sidianneng/xiaomi_temp_humi/source_code/Core/Inc/EPD_Font.h

#ifndef _EPD_FONT_H_
#define _EPD_FONT_H_


//图片取模配置使用软件 PCtoLCD2002
//点阵格式:阴码
//取模走向:逆向(低位在前)
//取模方式:
//				 字符:列行式 C51格式 
//				 中文:逐行式 C51格式
//字符尺寸限制:字符宽度限制为8的倍数

const unsigned char asc2_2412[][36]={	  
{0x00,0x00,0x00,0x00,0x00,0x00,0x00,0x00,0x00,0x00,0x00,0x00,0x00,0x00,0x00,0x00,0x00,0x00,0x00,0x00,0x00,0x00,0x00,0x00,0x00,0x00,0x00,0x00,0x00,0x00,0x00,0x00,0x00,0x00,0x00,0x00},/*" ",0*/
{0x00,0x00,0x00,0x00,0x00,0xF0,0xF0,0xF0,0x00,0x00,0x00,0x00,0x00,0x00,0x00,0x00,0x00,0x01,0x7F,0x01,0x00,0x00,0x00,0x00,0x00,0x00,0x00,0x00,0x00,0x1C,0x1C,0x1C,0x00,0x00,0x00,0x00},/*"!",1*/
{0x00,0x00,0x80,0x60,0x30,0x1C,0x8C,0x60,0x30,0x1C,0x0C,0x00,0x00,0x00,0x00,0x00,0x00,0x00,0x00,0x00,0x00,0x00,0x00,0x00,0x00,0x00,0x00,0x00,0x00,0x00,0x00,0x00,0x00,0x00,0x00,0x00},/*""",2*/
{0x00,0x00,0x00,0xE0,0x00,0x00,0x00,0x00,0x00,0xE0,0x00,0x00,0x00,0x86,0xE6,0x9F,0x86,0x86,0x86,0x86,0xE6,0x9F,0x86,0x00,0x00,0x01,0x1F,0x01,0x01,0x01,0x01,0x01,0x1F,0x01,0x01,0x00},/*"#",3*/
{0x00,0x00,0x80,0xC0,0x60,0x20,0xF8,0x20,0xE0,0xC0,0x00,0x00,0x00,0x00,0x03,0x07,0x0C,0x18,0xFF,0x70,0xE1,0x81,0x00,0x00,0x00,0x00,0x07,0x0F,0x10,0x10,0x7F,0x10,0x0F,0x07,0x00,0x00},/*"$",4*/
{0x80,0x60,0x20,0x60,0x80,0x00,0x00,0x00,0xE0,0x20,0x00,0x00,0x0F,0x30,0x20,0x30,0x9F,0x70,0xDC,0x37,0x10,0x30,0xC0,0x00,0x00,0x00,0x10,0x0E,0x03,0x00,0x07,0x18,0x10,0x18,0x07,0x00},/*"%",5*/
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
0x00,0x00,0x00,0x00,0x00,0x00,0x00,0x00,0x00,0x00,0x00,0x00,0x00,0x00,0x00,0x00},/*")",9*/
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
};

#endif
