sidianneng/xiaomi_temp_humi/source_code/Core/Inc/config.h

#ifndef __CONFIG_H__
#define __CONFIG_H__

#ifdef __cplusplus
extern "C" {
#endif

#define MAIN_VERSION 0x00
#define SUB_VERSION 0x01

#define DEBUG_LOG 1 
#define MAX_LOG_BUF_LEN 32U

#ifdef __cplusplus
}
#endif

#endif
