sidianneng/xiaomi_temp_humi/source_code/Core/Inc/Pic.h

#ifndef _PIC_H_
#define _PIC_H_

const unsigned char gImage_2424_bt[72] = { /* 0X01,0X01,0X18,0X00,0X18,0X00, */
0X00,0X00,0X00,0X00,0X00,0X00,0X00,0X00,0X00,0X00,0X00,0X00,0X00,0X00,0X00,0X03,
0X00,0XC0,0X01,0X81,0X80,0X00,0XC3,0X00,0X00,0X66,0X00,0X00,0X3C,0X00,0X00,0X18,
0X00,0X7F,0XFF,0XFE,0XFF,0XFF,0XFF,0XC0,0X3C,0X03,0X60,0X66,0X06,0X30,0XC3,0X0C,
0X19,0X81,0X98,0X0F,0X00,0XF0,0X06,0X00,0X60,0X00,0X00,0X00,0X00,0X00,0X00,0X00,
0X00,0X00,0X00,0X00,0X00,0X00,0X00,0X00,};

const unsigned char gImage_2424_nobt[72] = { /* 0X01,0X01,0X18,0X00,0X18,0X00, */
0X00,0X00,0X00,0X00,0X00,0X00,0X00,0X00,0X00,0X00,0X00,0X00,0X00,0X00,0X00,0X00,
0X00,0X00,0X00,0X00,0X00,0X00,0X00,0X00,0X00,0X00,0X00,0X00,0X00,0X00,0X00,0X00,
0X00,0X00,0X00,0X00,0X00,0X00,0X00,0X00,0X00,0X00,0X00,0X00,0X00,0X00,0X00,0X00,
0X00,0X00,0X00,0X00,0X00,0X00,0X00,0X00,0X00,0X00,0X00,0X00,0X00,0X00,0X00,0X00,
0X00,0X00,0X00,0X00,0X00,0X00,0X00,0X00,};

const unsigned char gImage_2424_bat[72] = { /* 0X01,0X01,0X18,0X00,0X18,0X00, */
0X00,0X00,0X00,0X00,0X00,0X00,0X00,0XFE,0X00,0X00,0XFE,0X00,0X07,0XFF,0XC0,0X04,
0X00,0X40,0X04,0X00,0X40,0X04,0X00,0X40,0X04,0X00,0X40,0X04,0X00,0X40,0X04,0X00,
0X40,0X04,0X00,0X40,0X04,0X00,0X40,0X04,0X00,0X40,0X04,0X00,0X40,0X04,0X00,0X40,
0X04,0X00,0X40,0X05,0XFF,0X40,0X05,0XFF,0X40,0X05,0XFF,0X40,0X04,0X00,0X40,0X07,
0XFF,0XC0,0X03,0XFF,0X80,0X00,0X00,0X00,};

const unsigned char gImage_2424_nobat[72] = { /* 0X01,0X01,0X18,0X00,0X18,0X00, */
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
0X00,0X00,0X00,0X00,0X00,0X00,0X00,0X00,0X00,0X00,0X00,0X00,0X00,0X00,0X00,0X00,
0X00,0X00,0X00,0X00,0X00,0X00,0X00,0X00,0X1E,0X00,0X00,0X38,0X1F,0X80,0X01,0XF8,
0X0F,0XFF,0XFF,0XF0,0X01,0XFF,0XFF,0X80,0X00,0X1F,0XF8,0X00,0X00,0X00,0X00,0X00,
};

#endif
