sidianneng/xiaomi_temp_humi/source_code/Core/Src/usart.c

/**
  ******************************************************************************
  * @file    usart.c
  * @brief   This file provides code for the configuration
  *          of the USART instances.
  ******************************************************************************
  * @attention
  *
  * <h2><center>&copy; Copyright (c) 2024 STMicroelectronics.
  * All rights reserved.</center></h2>
  *
  * This software component is licensed by ST under BSD 3-Clause license,
  * the "License"; You may not use this file except in compliance with the
  * License. You may obtain a copy of the License at:
  *                        opensource.org/licenses/BSD-3-Clause
  *
  ******************************************************************************
  */

/* Includes ------------------------------------------------------------------*/
#include "usart.h"

/* USART2 init function */

void MX_USART2_UART_Init(void)
{

  LL_USART_InitTypeDef USART_InitStruct = {0};

  LL_GPIO_InitTypeDef GPIO_InitStruct = {0};

  /* Peripheral clock enable */
  LL_APB1_GRP1_EnableClock(LL_APB1_GRP1_PERIPH_USART2);

  /* Set USART1 clock source as HSI */
  LL_RCC_SetUSARTClockSource(LL_RCC_USART2_CLKSOURCE_HSI);

  LL_IOP_GRP1_EnableClock(LL_IOP_GRP1_PERIPH_GPIOA);
  /**USART2 GPIO Configuration
  PA2   ------> USART2_TX
  PA3   ------> USART2_RX
  */
  GPIO_InitStruct.Pin = LL_GPIO_PIN_2;
  GPIO_InitStruct.Mode = LL_GPIO_MODE_ALTERNATE;
  GPIO_InitStruct.Speed = LL_GPIO_SPEED_FREQ_VERY_HIGH;
  GPIO_InitStruct.OutputType = LL_GPIO_OUTPUT_PUSHPULL;
  GPIO_InitStruct.Pull = LL_GPIO_PULL_NO;
  GPIO_InitStruct.Alternate = LL_GPIO_AF_4;
  LL_GPIO_Init(GPIOA, &GPIO_InitStruct);

  GPIO_InitStruct.Pin = LL_GPIO_PIN_3;
  GPIO_InitStruct.Mode = LL_GPIO_MODE_ALTERNATE;
  GPIO_InitStruct.Speed = LL_GPIO_SPEED_FREQ_VERY_HIGH;
  GPIO_InitStruct.OutputType = LL_GPIO_OUTPUT_PUSHPULL;
  GPIO_InitStruct.Pull = LL_GPIO_PULL_NO;
  GPIO_InitStruct.Alternate = LL_GPIO_AF_4;
  LL_GPIO_Init(GPIOA, &GPIO_InitStruct);

  /* USART2 interrupt Init */
  NVIC_SetPriority(USART2_IRQn, 2);
  NVIC_EnableIRQ(USART2_IRQn);

  USART_InitStruct.BaudRate = 9600;
  USART_InitStruct.DataWidth = LL_USART_DATAWIDTH_8B;
  USART_InitStruct.StopBits = LL_USART_STOPBITS_1;
  USART_InitStruct.Parity = LL_USART_PARITY_NONE;
  USART_InitStruct.TransferDirection = LL_USART_DIRECTION_TX_RX;
  USART_InitStruct.HardwareFlowControl = LL_USART_HWCONTROL_NONE;
  USART_InitStruct.OverSampling = LL_USART_OVERSAMPLING_16;
  LL_USART_Init(USART2, &USART_InitStruct);
  LL_USART_ConfigAsyncMode(USART2);
  LL_USART_SetWKUPType(USART2, LL_USART_WAKEUP_ON_RXNE);
  LL_USART_Enable(USART2);
  /* USER CODE BEGIN USART2_Init 2 */

  LL_USART_EnableIT_RXNE(USART2);
  /* Polling USART initialisation */
  while((!(LL_USART_IsActiveFlag_TEACK(USART2))) || (!(LL_USART_IsActiveFlag_REACK(USART2))))
  { 
  }
  /* USER CODE END USART2_Init 2 */

}

/* USER CODE BEGIN 1 */
void PrepareUSARTToStopMode(void)
{

  /* Empty RX Fifo before entering Stop mode (Otherwise, characters already present in FIFO
     will lead to immediate wake up */
  while (LL_USART_IsActiveFlag_RXNE(USART2))
  {
    /* Read Received character. RXNE flag is cleared by reading of RDR register */
    LL_USART_ReceiveData8(USART2);
  }

  /* Clear OVERRUN flag */
  LL_USART_ClearFlag_ORE(USART2);

  /* Make sure that no USART transfer is on-going */ 
  while(LL_USART_IsActiveFlag_BUSY(USART2) == 1)
  {
  }
  /* Make sure that USART is ready to receive */   
  while(LL_USART_IsActiveFlag_REACK(USART2) == 0)
  {
  }

  /* Configure USART2 transfer interrupts : */
  /* Clear WUF flag and enable the UART Wake Up from stop mode Interrupt */
  LL_USART_ClearFlag_WKUP(USART2);
  LL_USART_EnableIT_WKUP(USART2);

  /* Enable Wake Up From Stop */
  LL_USART_EnableInStopMode(USART2);
}
/* USER CODE END 1 */

/************************ (C) COPYRIGHT STMicroelectronics *****END OF FILE****/
