sidianneng/xiaomi_temp_humi/source_code/Core/Src/i2c.c

/**
  ******************************************************************************
  * @file    i2c.c
  * @brief   This file provides code for the configuration
  *          of the I2C instances.
  ******************************************************************************
  * @attention
  *
  * <h2><center>&copy; Copyright (c) 2024 STMicroelectronics.
  * All rights reserved.</center></h2>
  *
  * This software component is licensed by ST under BSD 3-Clause license,
  * the "License"; You may not use this file except in compliance with the
  * License. You may obtain a copy of the License at:
  *                        opensource.org/licenses/BSD-3-Clause
  *
  ******************************************************************************
  */

/* Includes ------------------------------------------------------------------*/
#include "i2c.h"

/* I2C1 init function */
void MX_I2C1_Init(void)
{

  LL_I2C_InitTypeDef I2C_InitStruct = {0};

  LL_GPIO_InitTypeDef GPIO_InitStruct = {0};

  uint32_t timing = 0;

  LL_IOP_GRP1_EnableClock(LL_IOP_GRP1_PERIPH_GPIOA);
  /**I2C1 GPIO Configuration
  PA9   ------> I2C1_SCL
  PA10   ------> I2C1_SDA
  */
  GPIO_InitStruct.Pin = LL_GPIO_PIN_9;
  GPIO_InitStruct.Mode = LL_GPIO_MODE_ALTERNATE;
  GPIO_InitStruct.Speed = LL_GPIO_SPEED_FREQ_VERY_HIGH;
  GPIO_InitStruct.OutputType = LL_GPIO_OUTPUT_OPENDRAIN;
  GPIO_InitStruct.Pull = LL_GPIO_PULL_UP;
  GPIO_InitStruct.Alternate = LL_GPIO_AF_1;
  LL_GPIO_Init(GPIOA, &GPIO_InitStruct);

  GPIO_InitStruct.Pin = LL_GPIO_PIN_10;
  GPIO_InitStruct.Mode = LL_GPIO_MODE_ALTERNATE;
  GPIO_InitStruct.Speed = LL_GPIO_SPEED_FREQ_VERY_HIGH;
  GPIO_InitStruct.OutputType = LL_GPIO_OUTPUT_OPENDRAIN;
  GPIO_InitStruct.Pull = LL_GPIO_PULL_UP;
  GPIO_InitStruct.Alternate = LL_GPIO_AF_1;
  LL_GPIO_Init(GPIOA, &GPIO_InitStruct);

  /* Peripheral clock enable */
  LL_APB1_GRP1_EnableClock(LL_APB1_GRP1_PERIPH_I2C1);

  /* According to TRM, I2C clock must be HSI if it can wakeup STOP mode */
  LL_RCC_SetI2CClockSource(LL_RCC_I2C1_CLKSOURCE_HSI);

  /* I2C1 interrupt Init */
  NVIC_SetPriority(I2C1_IRQn, 0);
  NVIC_EnableIRQ(I2C1_IRQn);

  /* USER CODE BEGIN I2C1_Init 1 */

  LL_I2C_Disable(I2C1);

  LL_I2C_EnableAutoEndMode(I2C1);
  LL_I2C_DisableOwnAddress2(I2C1);
  LL_I2C_EnableGeneralCall(I2C1);
  LL_I2C_DisableClockStretching(I2C1);

  timing = __LL_I2C_CONVERT_TIMINGS(0x0, 0x3, 0x0, 0x3d, 0x5b); 
  LL_I2C_SetTiming(I2C1, timing);

  LL_I2C_SetOwnAddress1(I2C1, (0x3c << 1), LL_I2C_OWNADDRESS1_7BIT);
  LL_I2C_EnableOwnAddress1(I2C1);

  //LL_I2C_EnableWakeUpFromStop(I2C1);

  LL_I2C_Enable(I2C1);

  /* Only ADDR match irq can wakeup STOP */
  LL_I2C_EnableIT_ADDR(I2C1);
  LL_I2C_EnableIT_RX(I2C1);
  LL_I2C_EnableIT_STOP(I2C1);
  /* USER CODE END I2C1_Init 2 */

}

/************************ (C) COPYRIGHT STMicroelectronics *****END OF FILE****/
