sidianneng/xiaomi_temp_humi/source_code/Core/Inc/EPD.h

#ifndef _EPD_H_
#define _EPD_H_

#include "SPI_Init.h"

#define EPD_W	152 
#define EPD_H	152

#define WHITE 0xFF
#define BLACK 0x00

#define delay_ms LL_mDelay

void EPD_READBUSY(void);
void EPD_HW_RESET(void);
void EPD_Update(void);
void EPD_PartUpdate(void);
void EPD_FastUpdate(void);
void EPD_DeepSleep(void);
void EPD_Init(void);
void EPD_FastMode1Init(void);
void EPD_FastMode2Init(void);
void EPD_Display_Clear(void);
void EPD_Clear_R26H(void);
void EPD_Display(const uint8_t *image);
#endif
